nikita-bretschneider/drirr_predregulace/3D/drirr_predreg5.png

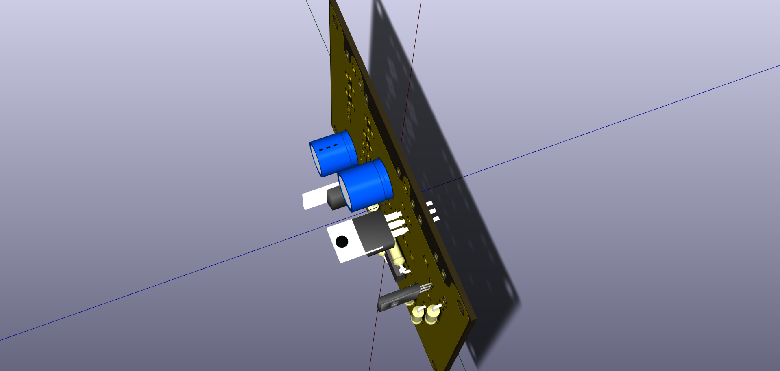
3D/drirr_predreg5.png
