nikita-bretschneider/drirr_predregulace/3D/drirr_predreg6.png

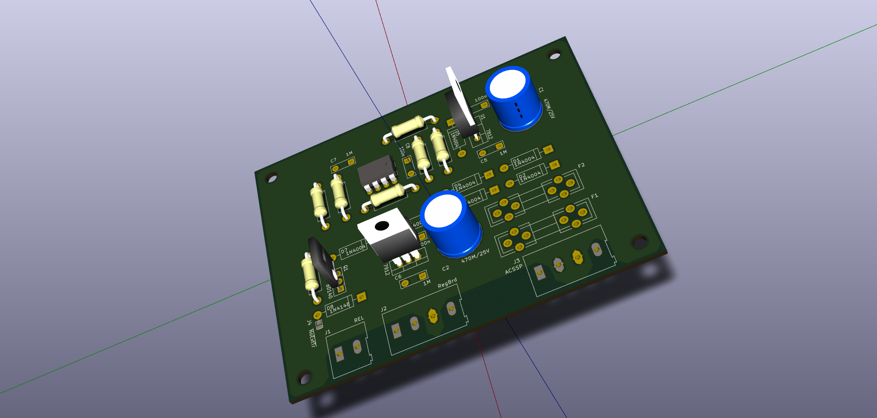
3D/drirr_predreg6.png
