nikita-bretschneider/drirr_predregulace/3D/drirr_predreg8.png

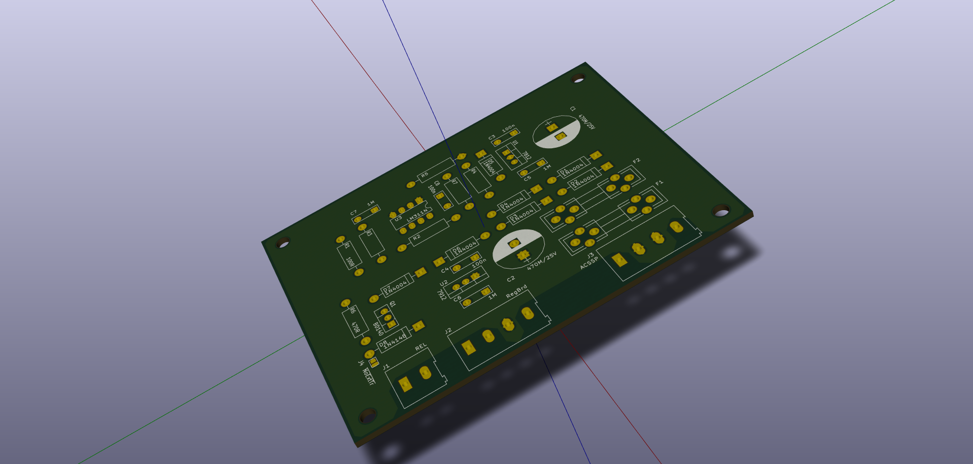
3D/drirr_predreg8.png
