nikita-bretschneider/drirr_predregulace/3D/drirr_predreg9.png

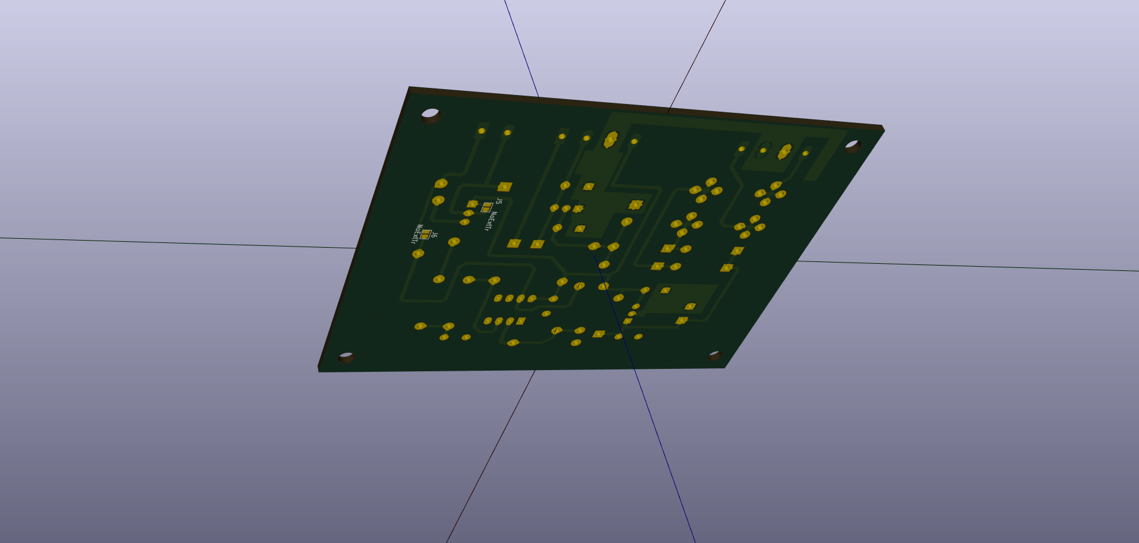
3D/drirr_predreg9.png
