nikita-bretschneider/drirr_predregulace/3D/drirr_predregB.png

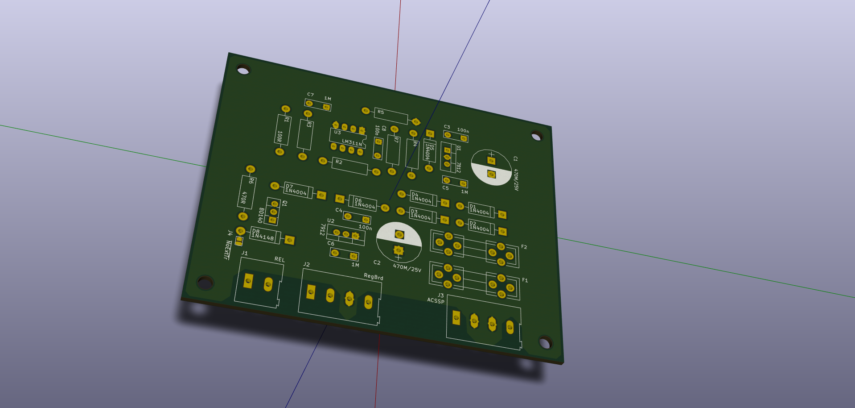
3D/drirr_predregB.png
